mjoldfield/car-battery-monitor/code/secrets.py

secrets = {
    'ssid' :       'WIFI NAME HERE',
    'password' :   'WIFI PASSWORD HERE',
    'smtp_server': 'IP ADDRESS OF SMTP SERVER',
    'mail_from':   'EMAIL ADDRESS',
    'mail_to':     'EMAIL ADDRESS',
    'subject':     'WHATEVER YOU LIKE'
}
